Asongnabrilan-nso/dorbel/media/product/Dorbel2.jpg

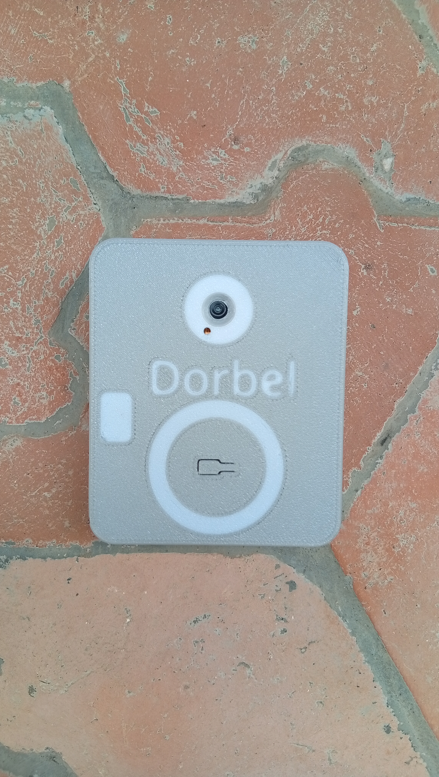
media/product/Dorbel2.jpg
