Asongnabrilan-nso/dorbel/media/product/Dorbel4.jpg

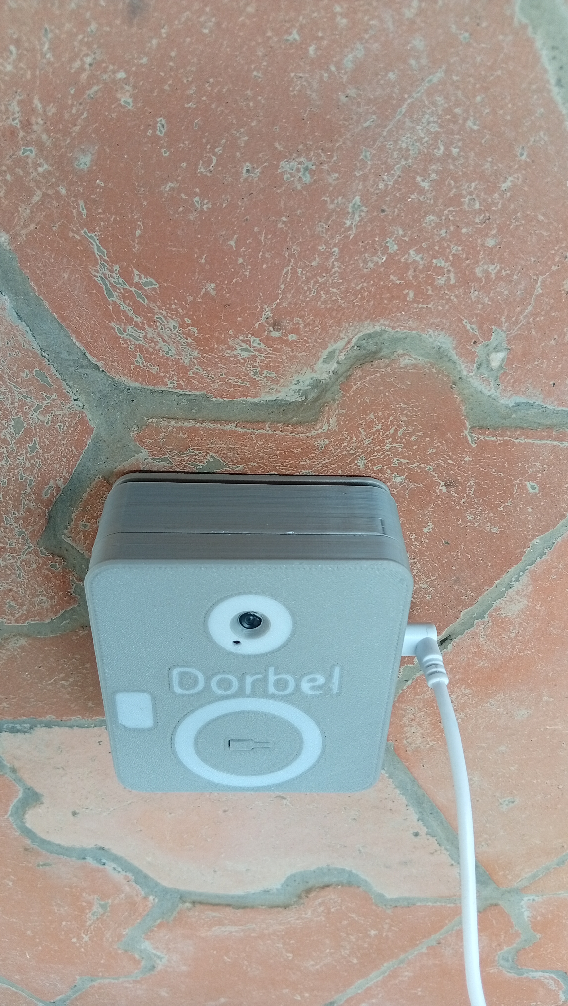
media/product/Dorbel4.jpg
