Asongnabrilan-nso/dorbel/media/product/Dorbel6.jpg

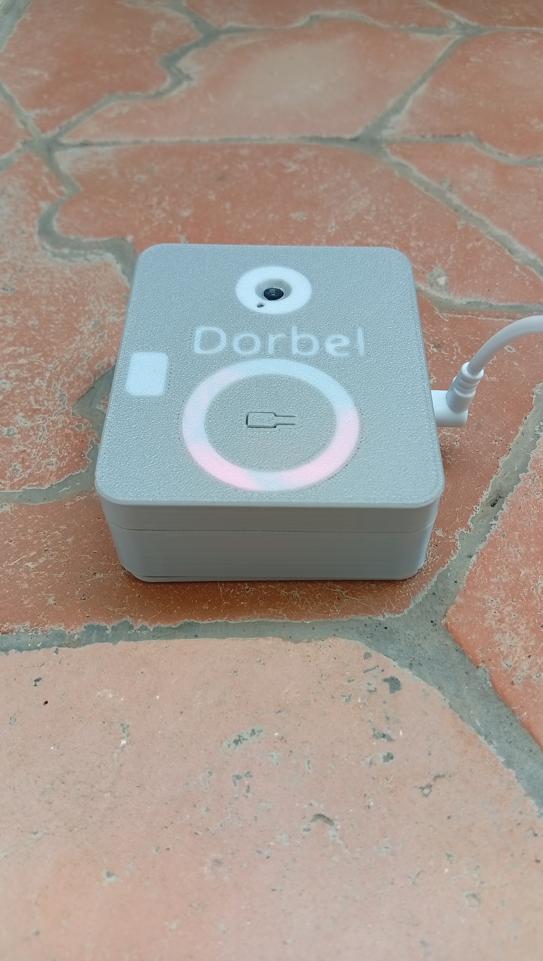
media/product/Dorbel6.jpg
