Asongnabrilan-nso/dorbel/media/product/mount-wall1.jpg

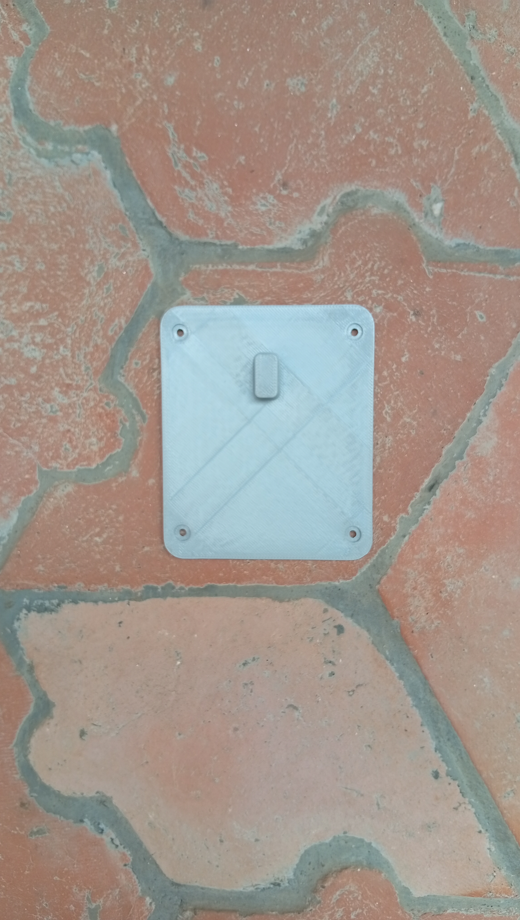
media/product/mount-wall1.jpg
