Asongnabrilan-nso/dorbel/media/product/mount-wall2.jpg

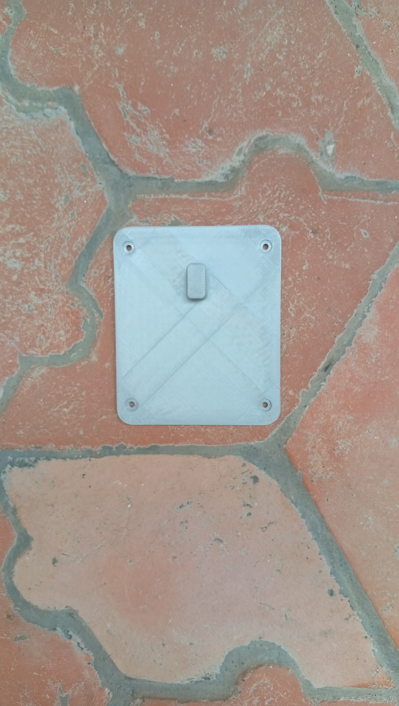
media/product/mount-wall2.jpg
