Asongnabrilan-nso/dorbel/media/product/photo_2026-10-05_17-58-14.jpg

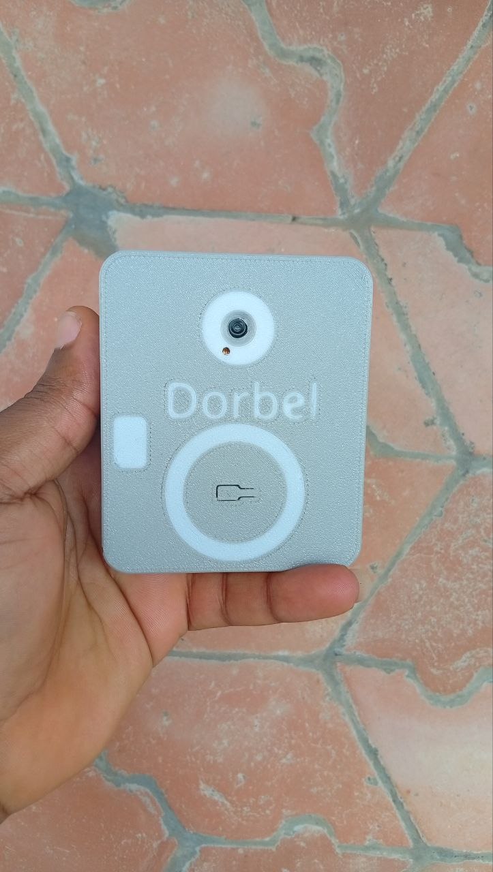
media/product/photo_2026-10-05_17-58-14.jpg
