Asongnabrilan-nso/dorbel/media/assembly/IMG_20261004_082605.jpg

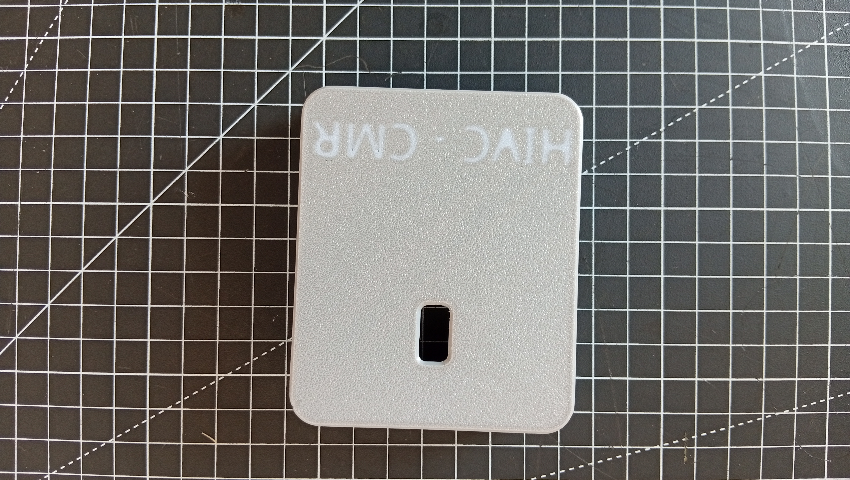
media/assembly/IMG_20261004_082605.jpg
